glhughes123/ledload/models/led rack mount-front with bezel.3mf

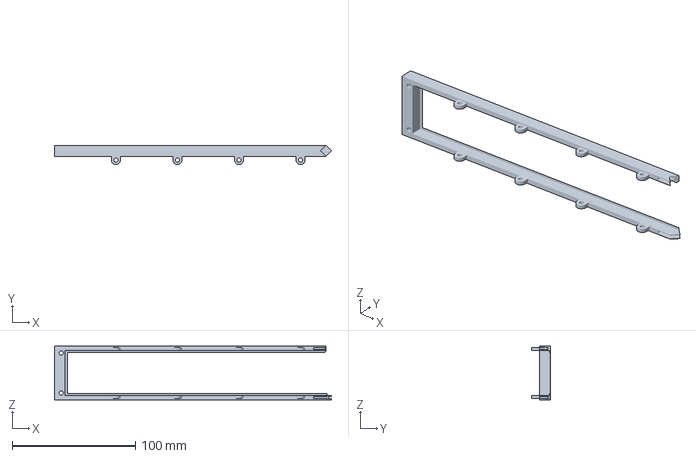
[picture p29: CAD file, 2025-02-27]
models/led rack mount-front with bezel.3mf
225.0 x 15.6 x 43.5 mm
