glhughes123/ledload/models/led alignment plate-7 leds w_ notches and edge.3mf

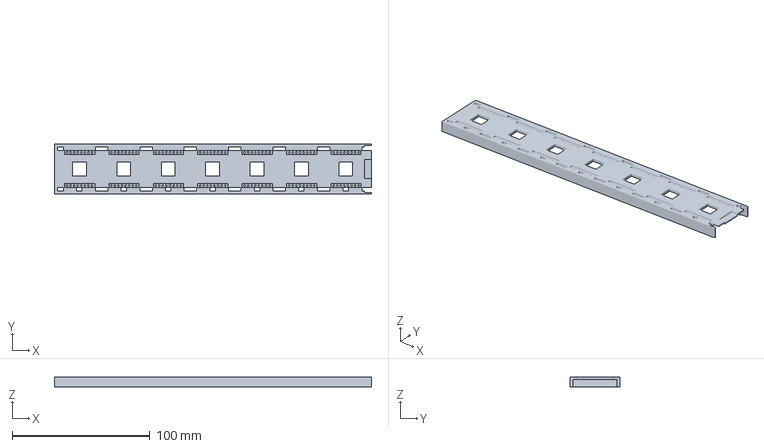
[picture p30: CAD file, 2025-02-27]
models/led alignment plate-7 leds w_ notches and edge.3mf
230.2 x 36.3 x 7.50 mm
