glhughes123/ledload/models/led rack mount-backplate with ethernet.3mf

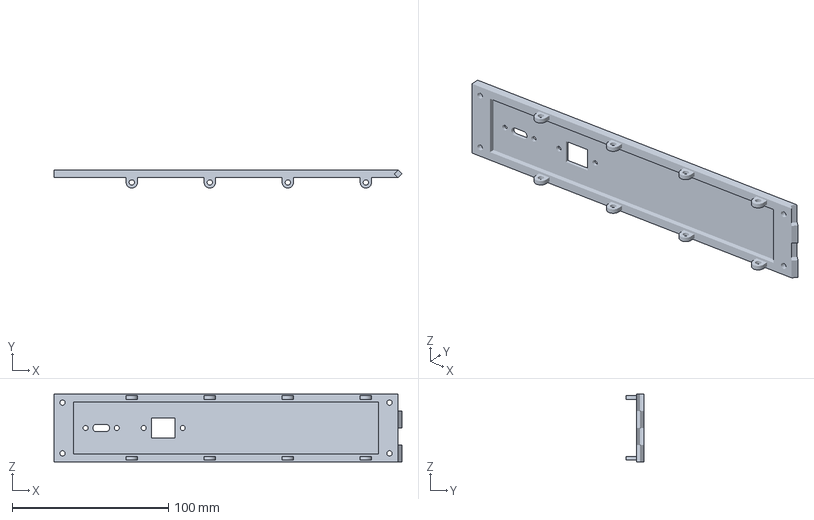
[picture p31: CAD file, 2025-02-27]
models/led rack mount-backplate with ethernet.3mf
223.0 x 11.6 x 43.5 mm
