glhughes123/ledload/models/led rack mount-panel 002 top with pins.3mf

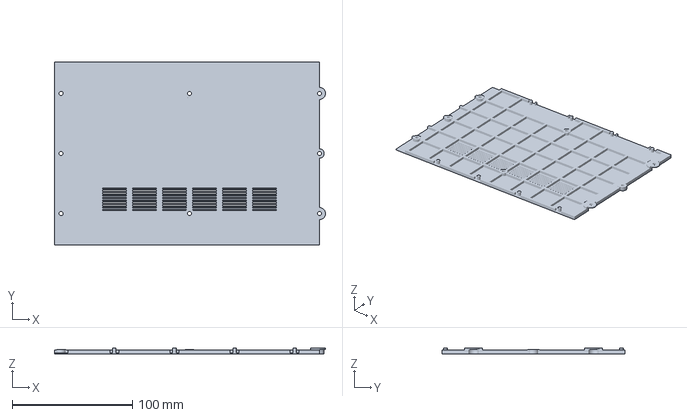
[picture p32: CAD file, 2025-02-27]
models/led rack mount-panel 002 top with pins.3mf
225.5 x 152.5 x 5.25 mm
