glhughes123/ledload/models/led rack mount-rpi4 mount.3mf

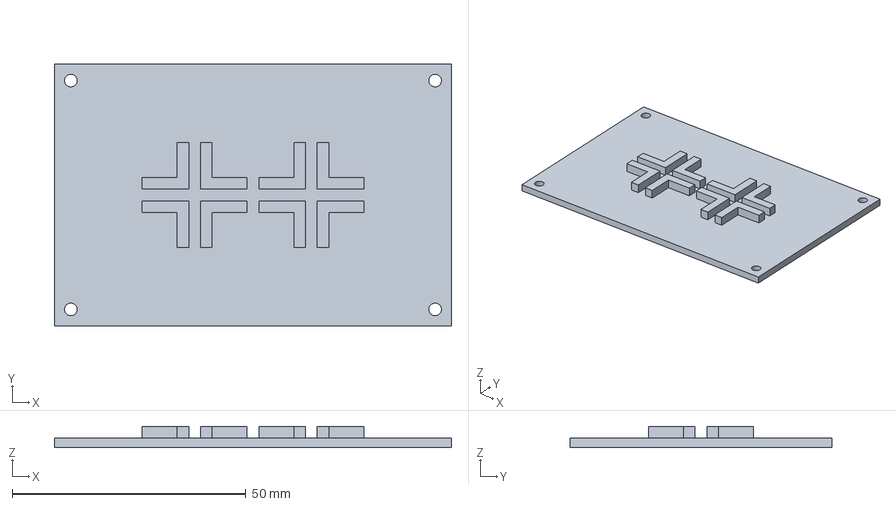
[picture p33: CAD file, 2025-02-27]
models/led rack mount-rpi4 mount.3mf
85.0 x 56.0 x 4.50 mm
