glhughes123/ledload/models/led rack mount-front center tab.3mf

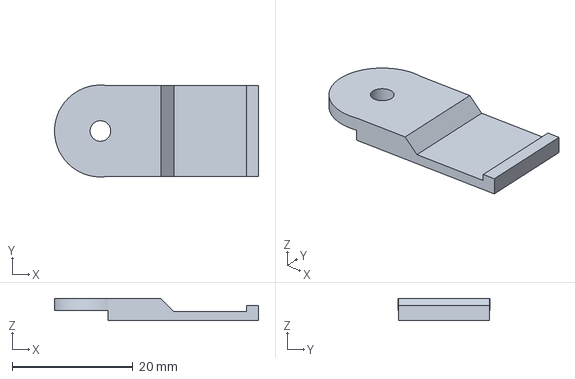
[picture p34: CAD file, 2025-02-27]
models/led rack mount-front center tab.3mf
33.8 x 15.2 x 3.65 mm
