glhughes123/ledload/models/led rack mount-panel 001 bottom with pins.3mf

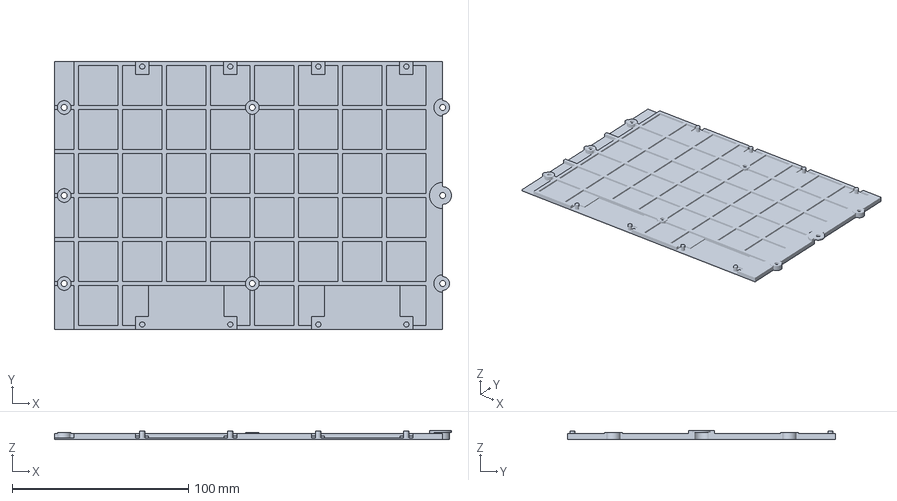
[picture p35: CAD file, 2025-02-27]
models/led rack mount-panel 001 bottom with pins.3mf
225.5 x 152.5 x 5.25 mm
