glhughes123/ledload/digits.h

#define DIGIT_WIDTH   8
#define DIGIT_HEIGHT  8

static char digits[16][DIGIT_HEIGHT][DIGIT_WIDTH + 1] =
{
    {
        " *****  ",
        "**   ** ",
        "**  *** ",
        "** **** ",
        "**** ** ",
        "***  ** ",
        " *****  ",
        "        ",
    },
    {
        "  **    ",
        " ***    ",
        "  **    ",
        "  **    ",
        "  **    ",
        "  **    ",
        "******  ",
        "        ",
    },
    {
        " ****   ",
        "**  **  ",
        "    **  ",
        "  ***   ",
        " **     ",
        "**  **  ",
        "******  ",
        "        ",
    },
    {
        " ****   ",
        "**  **  ",
        "    **  ",
        "  ***   ",
        "    **  ",
        "**  **  ",
        " ****   ",
        "        ",
    },
    {
        "   ***  ",
        "  ****  ",
        " ** **  ",
        "**  **  ",
        "******* ",
        "    **  ",
        "   **** ",
        "        ",
    },
    {
        "******  ",
        "**      ",
        "*****   ",
        "    **  ",
        "    **  ",
        "**  **  ",
        " ****   ",
        "        ",
    },
    {
        "  ***   ",
        " **     ",
        "**      ",
        "*****   ",
        "**  **  ",
        "**  **  ",
        " ****   ",
        "        ",
    },
    {
        "******  ",
        "**  **  ",
        "    **  ",
        "   **   ",
        "  **    ",
        "  **    ",
        "  **    ",
        "        ",
    },
    {
        " ****   ",
        "**  **  ",
        "**  **  ",
        " ****   ",
        "**  **  ",
        "**  **  ",
        " ****   ",
        "        ",
    },
    {
        " ****   ",
        "**  **  ",
        "**  **  ",
        " *****  ",
        "    **  ",
        "    **  ",
        " ****   ",
        "        ",
    },
    {
        "  **    ",
        " ****   ",
        "**  **  ",
        "**  **  ",
        "******  ",
        "**  **  ",
        "**  **  ",
        "        ",
    },
    {
        "******  ",
        " **  ** ",
        " **  ** ",
        " *****  ",
        " **  ** ",
        " **  ** ",
        "******  ",
        "        ",
    },
    {
        "  ****  ",
        " **  ** ",
        "**      ",
        "**      ",
        "**      ",
        " **  ** ",
        "  ****  ",
        "        ",
    },
    {
        "*****   ",
        " ** **  ",
        " **  ** ",
        " **  ** ",
        " **  ** ",
        " ** **  ",
        "*****   ",
        "        ",
    },
    {
        "******* ",
        " **   * ",
        " ** *   ",
        " ****   ",
        " ** *   ",
        " **   * ",
        "******* ",
        "        ",
    },
    {
        "******* ",
        " **   * ",
        " ** *   ",
        " ****   ",
        " ** *   ",
        " **     ",
        "****    ",
        "        ",
    },
};
